jankae/VNA/Hardware/ADCFilter.asc

1n: cap; 100p
2k: res; 6k8
C1: cap; 330p
C2: cap; 330p
C3: cap; 330p
C4: cap; 330p
C5: cap; 1µ
C6: cap; 1µ
C7: cap; 0p7
C8: cap; 100p
L3: ind; 0n7
L4: ind; 0n7
R1: res; 220
R2: res; 220
R3: res; 6k8
R4: res; 0
R5: res; 200
R6: res; 200
R7: res; 1k2
R8: res; 0
R9: res; 220
R10: res; 220
U1: LTC6362
V1: voltage; SINE(0 0.27 250000); AC 1
V2: voltage; 5
Named nets: 0
;ac lin 1000 100k 1000k
.tran 100u
