jankae/VNA/Hardware/IF1Filter.asc

C1: cap; 0p4
C2: cap; 0p2
C3: cap; 120p
C4: cap; 150p
C5: cap; 33p
C6: cap; 10n
C7: cap; 10n
L1: ind; 1n2
L2: ind; 1n2
L3: ind; 68n
L4: ind; 68n
L5: ind; 33n
L6: ind; 33n
L7: ind; 2n
L8: ind; 2n
L11: ind; 330n
L12: ind; 330n
L13: ind; 330n
L14: ind; 330n
R1: res; 245
R2: res; 28.1
V1: voltage; ""; AC 1
Named nets: 0
.ac dec 1000 10000k 100000k
