jankae/VNA/RFExperiments/Software/RFExperiments/Application/Drivers/Si5351C.cpp

#include "Si5351C.hpp"

#include <cmath>

#define LOG_LEVEL	LOG_LEVEL_DEBUG
#define LOG_MODULE	"SI5351"
#include "Log.h"

bool Si5351C::Init(uint32_t clkin_freq) {
	bool success = true;

	uint8_t clkinDiv = 0;
	while (clkin_freq / (1 << clkinDiv) > 40000000) {
		if (clkinDiv < 3) {
			clkinDiv++;
		} else {
			LOG_ERR("CLK in too high");
			return false;
		}
	}
	FreqCLKINDiv = clkin_freq / (1 << clkinDiv);
	// Write CLK in divider
	uint8_t value;
	success &= ReadRegister(Reg::PLLInputSource, &value);
	value &= ~0xC0;
	value |= clkinDiv << 6;
	success &= WriteRegister(Reg::PLLInputSource, value);

	// Disable OEB pin functionality
	success &= WriteRegister(Reg::OEBPinMask, 0xFF);
	// Disable all outputs
	success &= WriteRegister(Reg::OutputEnableControl, 0xFF);

	// Enable fanouts
	success &= WriteRegister(Reg::FanoutEnable, 0xD0);

	if(success) {
		LOG_INFO("Initialized");
	} else {
		LOG_ERR("Initialization failed");
	}
	return success;
}

bool Si5351C::SetPLL(PLL pll, uint32_t frequency, PLLSource src) {
	if (frequency < 600000000 || frequency > 900000000) {
		LOG_ERR("Requested PLL frequency out of range (600-900MHz): %lu", frequency);
		return false;
	}
	PLLConfig c;
	c.IntegerMode = false;
	c.source = src;

	uint32_t srcFreq = src == PLLSource::XTAL ? FreqXTAL : FreqCLKINDiv;
	// see https://www.silabs.com/documents/public/application-notes/AN619.pdf (page 3)
	uint64_t div27 = (uint64_t) frequency * (1UL << 27) / srcFreq;
	// Check for valid range
	if (div27 < 15 * (1ULL << 27) || div27 > 90 * (1ULL << 27)) {
		LOG_ERR("Calculated divider out of range (15-90)");
		return false;
	}
	FindOptimalDivider(frequency, srcFreq, c.P1, c.P2, c.P3);

	FreqPLL[(int) pll] = frequency;
	LOG_INFO("Setting PLL %c to %luHz", pll==PLL::A ? 'A' : 'B', frequency);
	return WritePLLConfig(c, pll);
}

bool Si5351C::SetCLK(uint8_t clknum, uint32_t frequency, PLL source, DriveStrength strength, uint32_t PLLFreqOverride) {
	ClkConfig c;
	c.DivideBy4 = false;
	c.IntegerMode = false;
	c.Inverted = false;
	c.PoweredDown = false;
	c.RDiv = 1;
	c.source = source;
	c.strength = strength;

	uint32_t pllFreq = PLLFreqOverride > 0 ? PLLFreqOverride : FreqPLL[(int) source];
	if (clknum > 5) {
		// outputs 6 and 7 are integer dividers only
		uint32_t div = pllFreq / frequency;
		if (div > 254 || div < 6) {
			LOG_ERR("Divider on CLK6/7 out of range (6-254), would need %lu", div);
			return false;
		}
		if(div & 0x01) {
			LOG_ERR("Divider on CLK6/7 must be even, clock frequency will not match exactly");
		}
		div &= 0xFE;
		uint32_t actualFreq = pllFreq / div;
		LOG_DEBUG("Optimal divider for %luHz/%luHz is: %u (%luHz deviation)",
				pllFreq, frequency, div, abs(frequency - actualFreq));
		c.P1 = div;
	} else {
		while (pllFreq / (frequency * c.RDiv) >= 2048
				|| (frequency * c.RDiv) < 500000) {
			if (c.RDiv < 128) {
				c.RDiv *= 2;
			} else {
				LOG_ERR("Unable to reach requested frequency");
				return false;
			}
		}
		FindOptimalDivider(pllFreq, frequency * c.RDiv, c.P1, c.P2, c.P3);
	}
	LOG_INFO("Setting CLK%d to %luHz", clknum, frequency);
	return WriteClkConfig(c, clknum);
}

bool Si5351C::SetCLKtoXTAL(uint8_t clknum) {
	Reg reg = (Reg) ((int) Reg::CLK0Control + clknum);
	LOG_INFO("Connecting CLK%d to XTAL", clknum);
	return ClearBits(reg, 0x0C);
}
bool Si5351C::SetCLKToCLKIN(uint8_t clknum) {
	Reg reg = (Reg) ((int) Reg::CLK0Control + clknum);
	LOG_INFO("Connecting CLK%d to CLK in", clknum);
	return ClearBits(reg, 0x08) && SetBits(reg, 0x04);
}

bool Si5351C::Enable(uint8_t clknum) {
	LOG_INFO("Enabling CLK%d", clknum);
	return ClearBits(Reg::OutputEnableControl, 1 << clknum);
}

bool Si5351C::Disable(uint8_t clknum) {
	LOG_INFO("Disabling CLK%d", clknum);
	return SetBits(Reg::OutputEnableControl, 1 << clknum);
}

bool Si5351C::Locked(PLL pll) {
	uint8_t mask = pll == PLL::A ? 0x20 : 0x40;
	uint8_t value;
	ReadRegister(Reg::DeviceStatus, &value);
	LOG_DEBUG("Device status: 0x%02x", value);
	if (value & mask) {
		return false;
	} else {
		return true;
	}
}

bool Si5351C::WritePLLConfig(PLLConfig config, PLL pll) {
	uint8_t PllData[8];
	// See register map in https://www.silabs.com/documents/public/application-notes/AN619.pdf (page 11)
	PllData[0] = (config.P3 >> 8) & 0xFF;
	PllData[1] = config.P3 & 0xFF;
	PllData[2] = (config.P1 >> 16) & 0x03;
	PllData[3] = (config.P1 >> 8) & 0xFF;
	PllData[4] = config.P1 & 0xFF;
	PllData[5] = ((config.P3 >> 12) & 0xF0) | ((config.P2 >> 16) & 0x0F);
	PllData[6] = (config.P2 >> 8) & 0xFF;
	PllData[7] = config.P2 & 0xFF;
	bool success = true;
	Reg reg = pll == PLL::A ? Reg::MSNA_CONFIG : Reg::MSNB_CONFIG;
	success &= WriteRegisterRange(reg, PllData, sizeof(PllData));
	reg = pll == PLL::A ? Reg::CLK6Control : Reg::CLK7Control;
	if (config.IntegerMode) {
		success &=SetBits(reg, 0x40);
	} else {
		success &=ClearBits(reg, 0x40);
	}
	uint8_t mask = pll == PLL::A ? 0x04 : 0x08;
	if (config.source == PLLSource::XTAL) {
		success &=ClearBits(Reg::PLLInputSource, mask);
	} else {
		success &=SetBits(Reg::PLLInputSource, mask);
	}

	// Reset the PLL
	mask = pll == PLL::A ? 0x20 : 0x80;
	//success &=SetBits(Reg::PLLReset, mask);
	reg = pll == PLL::A ? Reg::MSNA_CONFIG : Reg::MSNB_CONFIG;
	for(uint8_t i=0;i<8;i++) {
		uint8_t readback;
		ReadRegister((Reg)((int)reg + i), &readback);
		LOG_DEBUG("PLL readback %d: 0x%02x", i, readback);
	}

	return success;
}

bool Si5351C::WriteClkConfig(ClkConfig config, uint8_t clknum) {
	bool success = true;
	// compile CLKControl register
	uint8_t clkcontrol = 0x0C;
	if (config.PoweredDown) {
		clkcontrol |= 0x80;
	}
	if (clknum <= 5) {
		if (config.IntegerMode) {
			clkcontrol |= 0x40;
		}
	} else {
		// preserve bit 6
		uint8_t value = 0x00;
		success &= ReadRegister((Reg) ((int) Reg::CLK0Control + clknum),
				&value);
		clkcontrol |= value & 0x40;
	}
	if (config.source == PLL::B) {
		clkcontrol |= 0x20;
	}
	if (config.Inverted) {
		clkcontrol |= 0x10;
	}
	switch (config.strength) {
	case DriveStrength::mA2:
		break;
	case DriveStrength::mA4:
		clkcontrol |= 0x01;
		break;
	case DriveStrength::mA6:
		clkcontrol |= 0x02;
		break;
	case DriveStrength::mA8:
		clkcontrol |= 0x03;
		break;
	}
	Reg reg = (Reg) ((int) Reg::CLK0Control + clknum);
	success &= WriteRegister(reg, clkcontrol);
	if (clknum <= 5) {
		uint8_t ClkData[8];
		ClkData[0] = (config.P3 >> 8) & 0xFF;
		ClkData[1] = config.P3 & 0xFF;
		ClkData[2] = (31 - __builtin_clz(config.RDiv)) << 4
				| (config.DivideBy4 ? 0xC0 : 0x00) | ((config.P1 >> 16) & 0x03);
		ClkData[3] = (config.P1 >> 8) & 0xFF;
		ClkData[4] = config.P1 & 0xFF;
		ClkData[5] = ((config.P3 >> 12) & 0xF0) | ((config.P2 >> 16) & 0x0F);
		ClkData[6] = (config.P2 >> 8) & 0xFF;
		ClkData[7] = config.P2 & 0xFF;
		// Calculate address of register control block
		reg = (Reg) ((int) Reg::MS0_CONFIG + 8 * clknum);
		success &= WriteRegisterRange(reg, ClkData, sizeof(ClkData));
	} else if (clknum == 6) {
		success &= WriteRegister(Reg::MS6_CONFIG, config.P1 & 0xFF);
	} else {
		success &= WriteRegister(Reg::MS7_CONFIG, config.P1 & 0xFF);
	}

	return success;
}

bool Si5351C::WriteRegister(Reg reg, uint8_t data) {
	return WriteRegisterRange(reg, &data, 1);
}

bool Si5351C::ReadRegister(Reg reg, uint8_t *data) {
	return HAL_I2C_Mem_Read(i2c, address, (int) reg,
	I2C_MEMADD_SIZE_8BIT, data, 1, 100) == HAL_OK;
}

bool Si5351C::SetBits(Reg reg, uint8_t bits) {
	uint8_t value = 0;
	if (!ReadRegister(reg, &value)) {
		return false;
	}
	value |= bits;
	return WriteRegister(reg, value);
}

bool Si5351C::ClearBits(Reg reg, uint8_t bits) {
	uint8_t value = 0;
	if (!ReadRegister(reg, &value)) {
		return false;
	}
	value &= ~bits;
	return WriteRegister(reg, value);
}

bool Si5351C::WriteRegisterRange(Reg start, uint8_t *data, uint8_t len) {
	return HAL_I2C_Mem_Write(i2c, address, (int) start,
	I2C_MEMADD_SIZE_8BIT, data, len, 100) == HAL_OK;
}

bool Si5351C::ResetPLLs() {
	return SetBits(Reg::PLLReset, 0xA0);
}

void Si5351C::FindOptimalDivider(uint32_t f_pll, uint32_t f, uint32_t &P1,
		uint32_t &P2, uint32_t &P3) {
	// see https://www.silabs.com/documents/public/application-notes/AN619.pdf (page 3/6)
	uint32_t a = f_pll / f;
	int32_t f_rem = f_pll - f * a;
	uint32_t best_b, best_c;
	uint32_t best_deviation = UINT32_MAX;
	for (uint32_t c = (1UL << 20) - 1; c >= (1UL << 19); c--) {
		uint32_t guess_b = (uint64_t) f_rem * c / f;
		for (uint32_t b = guess_b; b <= guess_b + 1; b++) {
			int32_t f_div = (uint64_t) f * b / c;
			uint32_t deviation = abs(f_rem - f_div);
			if (deviation < best_deviation) {
				best_b = b;
				best_c = c;
				best_deviation = deviation;
				if (deviation == 0) {
					break;
				}
			}
		}
		if (best_deviation == 0) {
			break;
		}
	}
	LOG_DEBUG(
			"Optimal divider for %luHz/%luHz is: a=%lu, b=%lu, c=%lu (%luHz deviation)",
			f_pll, f, a, best_b, best_c, best_deviation);
	// convert to Si5351C parameters
	uint32_t floor = 128 * best_b / best_c;
	P1 = 128 * a + floor - 512;
	P2 = 128 * best_b - best_c * floor;
	P3 = best_c;
	LOG_DEBUG("P1=%lu, P2=%lu, P3=%lu", P1, P2, P3);
}
